Xamla/xamla_egomo/egomo_3d_printed_parts/egomo-1/xamla_mount_rpi_middle.stl

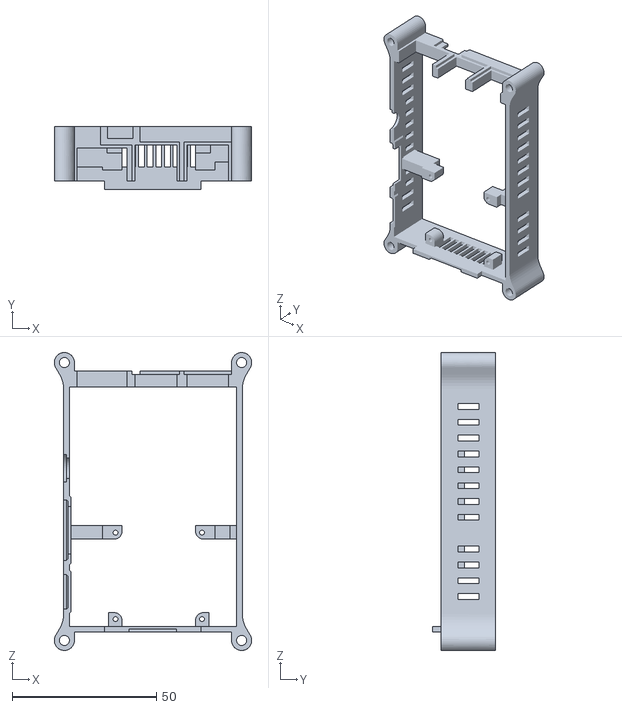
[picture p21: CAD file, 2016-06-17]
egomo_3d_printed_parts/egomo-1/xamla_mount_rpi_middle.stl
68.5 x 21.8 x 103.4
