Xamla/xamla_egomo/egomo_ur5/meshes/robotiq-2-finger-85/collision/gripper_finger_left_1.stl

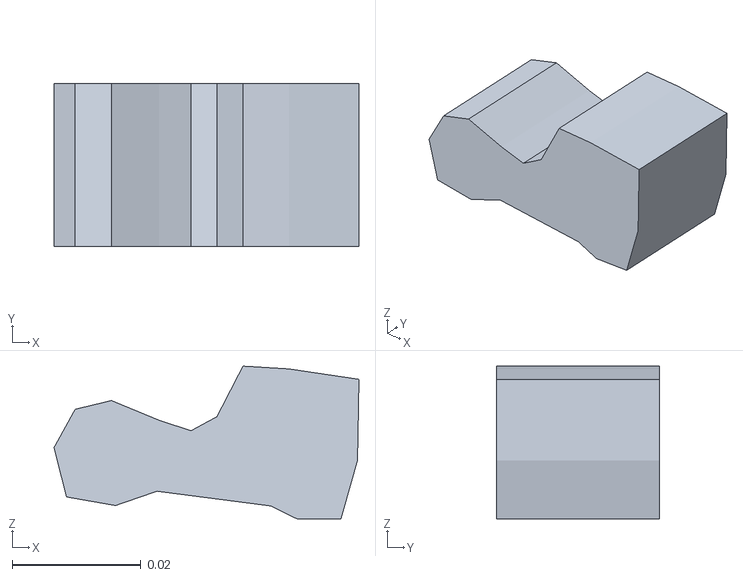
[picture p22: CAD file, 2016-05-12]
egomo_ur5/meshes/robotiq-2-finger-85/collision/gripper_finger_left_1.stl
0.0474 x 0.0254 x 0.0237
