Xamla/xamla_egomo/egomo_ur5/meshes/ur5/collision/wrist_2.stl

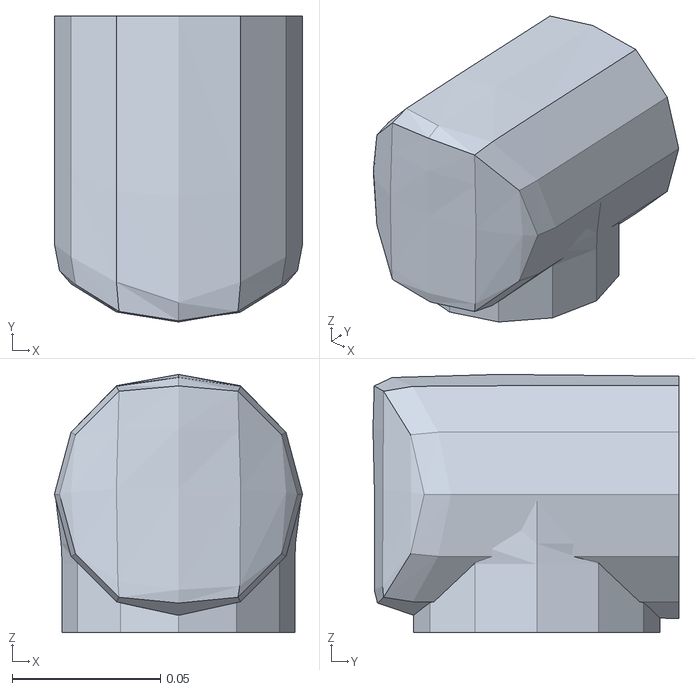
[picture p23: CAD file, 2016-05-12]
egomo_ur5/meshes/ur5/collision/wrist_2.stl
0.0837 x 0.103 x 0.0871
