Xamla/xamla_egomo/egomo_3d_printed_parts/egomo-1/xamla_mount_rpi_bottom.stl

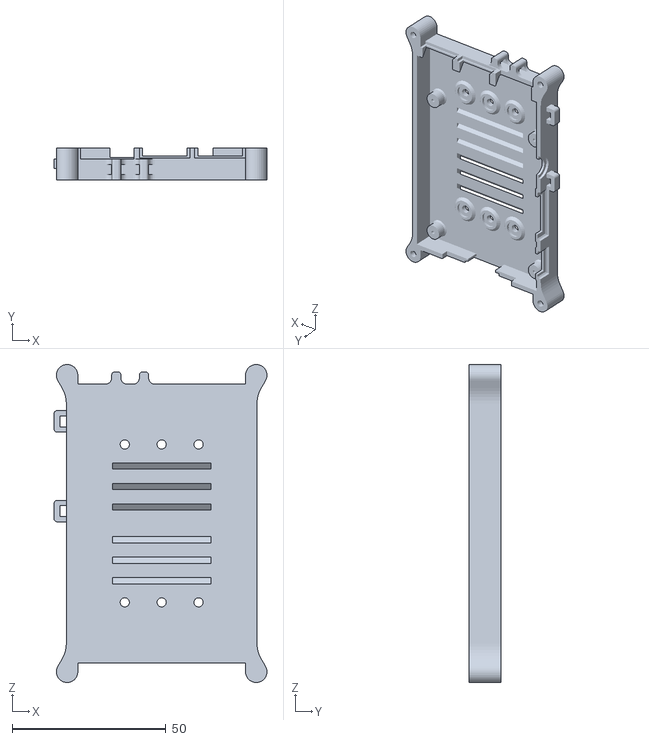
[picture p24: CAD file, 2016-06-17]
egomo_3d_printed_parts/egomo-1/xamla_mount_rpi_bottom.stl
69.2 x 10.3 x 103.4
