Xamla/xamla_egomo/egomo_ur5/meshes/robotiq-2-finger-85/collision/gripper_base.stl

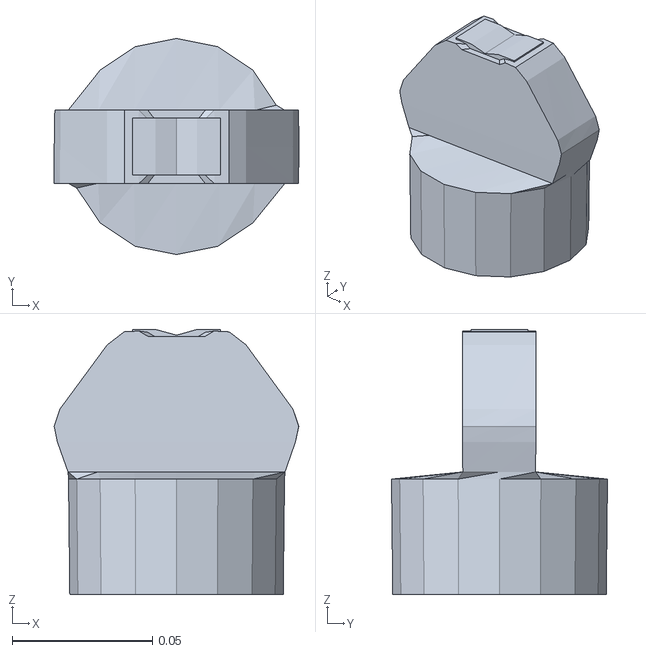
[picture p25: CAD file, 2016-05-12]
egomo_ur5/meshes/robotiq-2-finger-85/collision/gripper_base.stl
0.0874 x 0.0771 x 0.0946
