Xamla/xamla_egomo/egomo_ur5/meshes/ur5/collision/forearm.stl

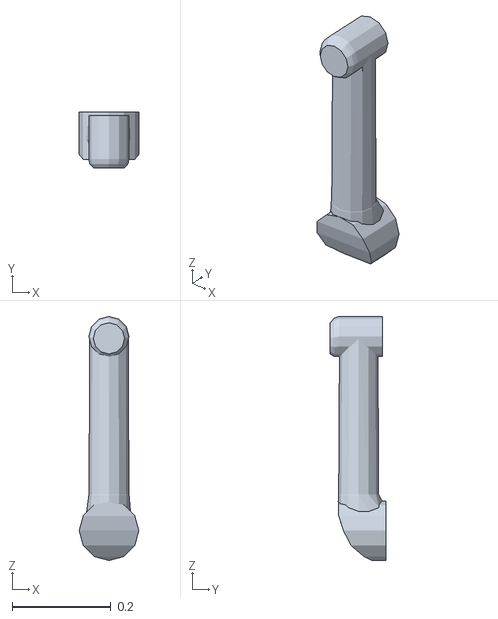
[picture p26: CAD file, 2016-05-12]
egomo_ur5/meshes/ur5/collision/forearm.stl
0.121 x 0.112 x 0.493
