Xamla/xamla_egomo/egomo_3d_printed_parts/egomo-1/xamla_mount_c920_front_0_right.stl

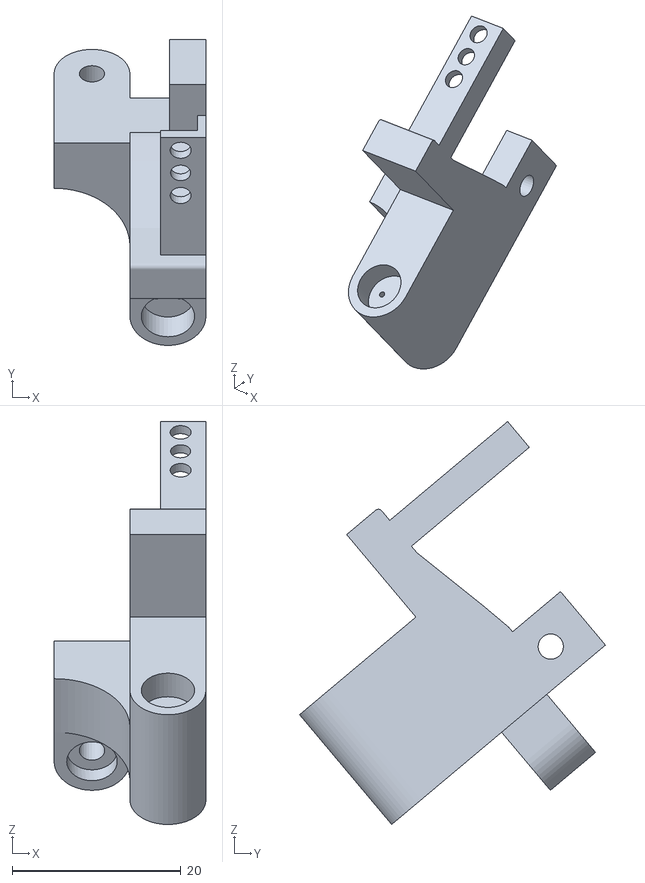
[picture p27: CAD file, 2016-06-17]
egomo_3d_printed_parts/egomo-1/xamla_mount_c920_front_0_right.stl
18.0 x 36.3 x 47.8
