Xamla/xamla_egomo/egomo_ur5/meshes/robotiq-2-finger-85/collision/gripper_finger_left_3.stl

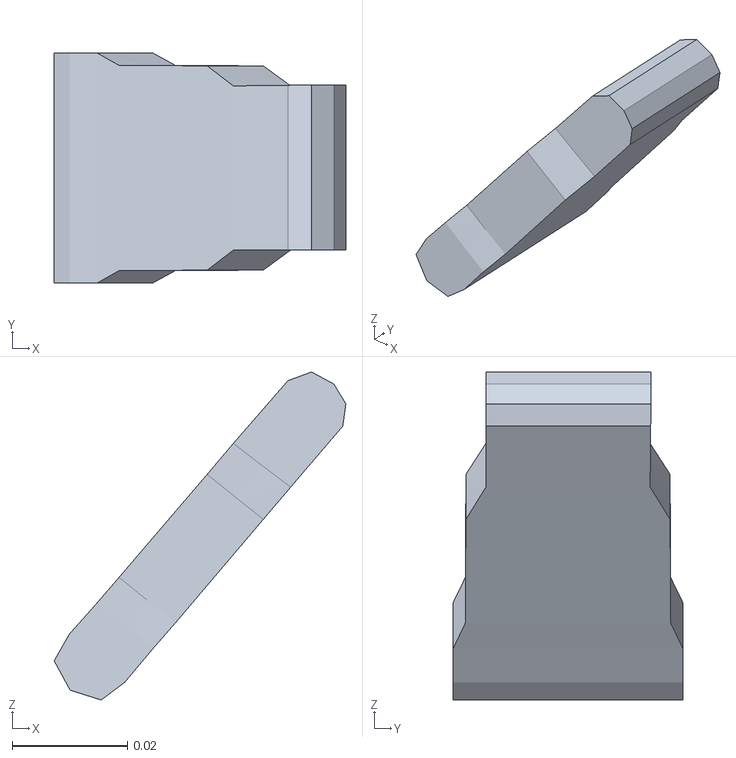
[picture p28: CAD file, 2016-05-12]
egomo_ur5/meshes/robotiq-2-finger-85/collision/gripper_finger_left_3.stl
0.0506 x 0.0398 x 0.0569
