Xamla/xamla_egomo/egomo_ur5/meshes/ur5/collision/wrist_1.stl

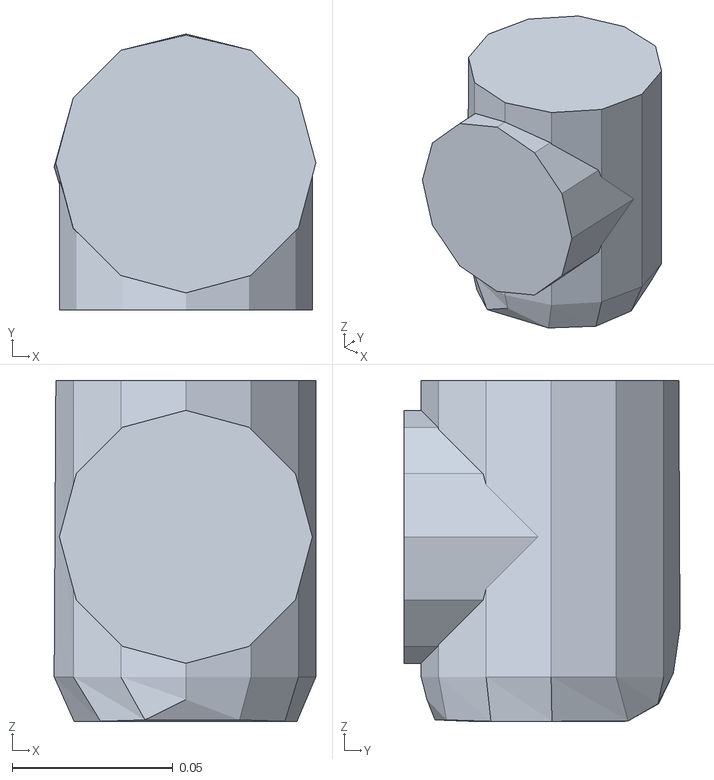
[picture p29: CAD file, 2016-05-12]
egomo_ur5/meshes/ur5/collision/wrist_1.stl
0.0815 x 0.0859 x 0.106
