Xamla/xamla_egomo/egomo_3d_printed_parts/egomo-1/xamla_cap_hole.stl

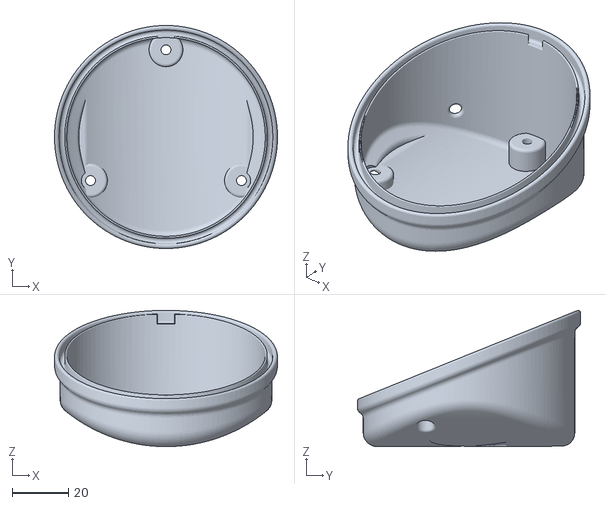
[picture p30: CAD file, 2016-06-17]
egomo_3d_printed_parts/egomo-1/xamla_cap_hole.stl
79.0 x 79.0 x 48.3
