Xamla/xamla_egomo/egomo_ur5/meshes/robotiq-2-finger-85/collision/gripper_finger_left_2.stl

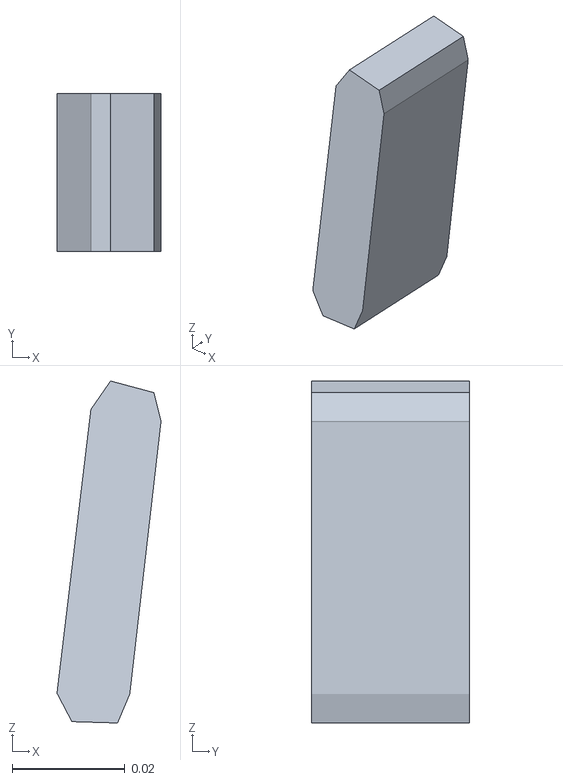
[picture p31: CAD file, 2016-05-12]
egomo_ur5/meshes/robotiq-2-finger-85/collision/gripper_finger_left_2.stl
0.0185 x 0.028 x 0.0607
