Xamla/xamla_egomo/egomo_3d_printed_parts/egomo-1/xamla_mount_c920_right.stl

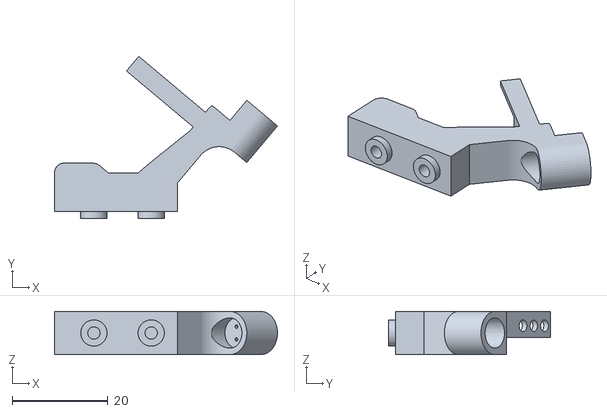
[picture p32: CAD file, 2016-06-17]
egomo_3d_printed_parts/egomo-1/xamla_mount_c920_right.stl
46.7 x 34.0 x 9.02
