Xamla/xamla_egomo/egomo_3d_printed_parts/egomo-1/xamla_mount_flange.stl

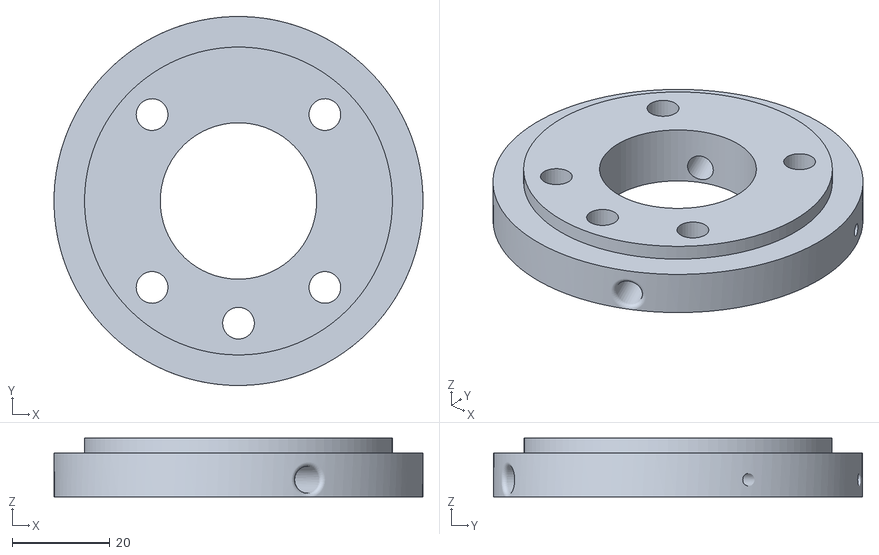
[picture p34: CAD file, 2016-06-17]
egomo_3d_printed_parts/egomo-1/xamla_mount_flange.stl
75.5 x 75.5 x 12.0
