Xamla/xamla_egomo/egomo_docs/Egomo_Installation/small-DSC03187.JPG

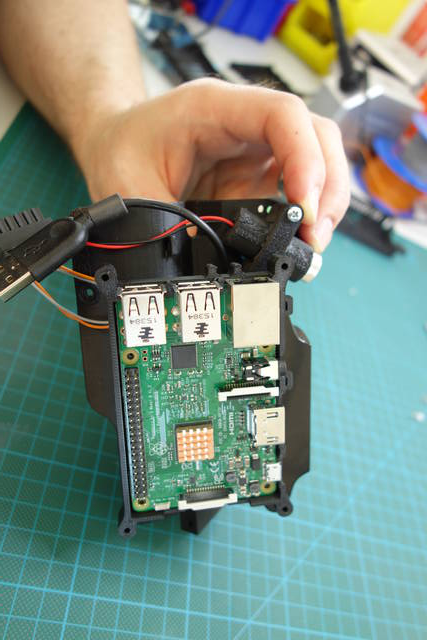
egomo_docs/Egomo_Installation/small-DSC03187.JPG
