Xamla/xamla_egomo/egomo_docs/Egomo_Installation/small-DSC03204.JPG

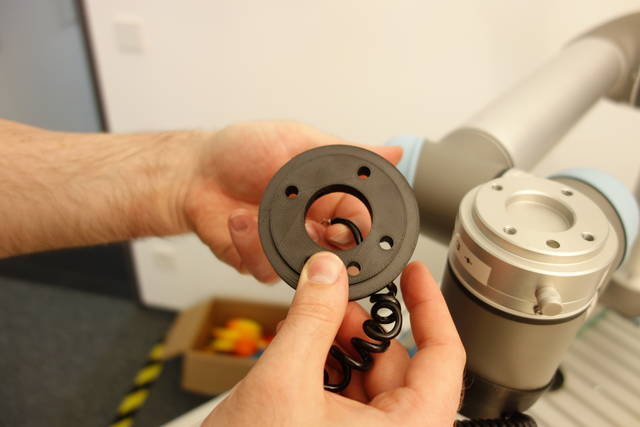
egomo_docs/Egomo_Installation/small-DSC03204.JPG
