Xamla/xamla_egomo/egomo_docs/Egomo_Installation/small-IMG_20160613_182819.jpg

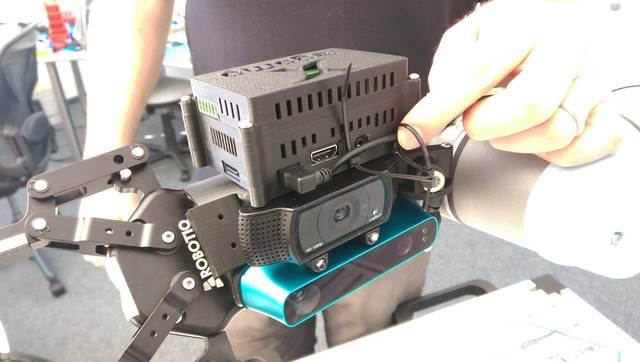
egomo_docs/Egomo_Installation/small-IMG_20160613_182819.jpg
