Xamla/xamla_egomo/egomo_docs/Egomo_Installation/small-IMG_20160613_182855.jpg

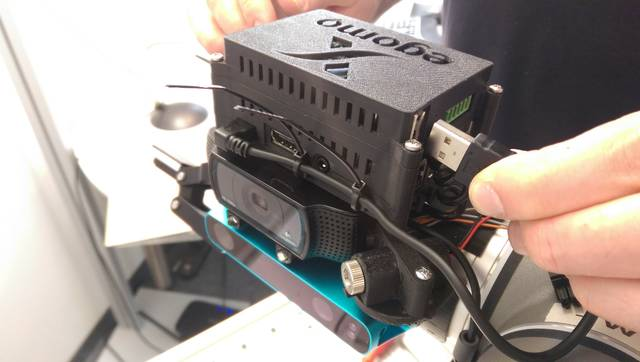
egomo_docs/Egomo_Installation/small-IMG_20160613_182855.jpg
