Xamla/xamla_egomo/egomo_docs/Egomo_Installation/small-IMG_20160613_183529.jpg

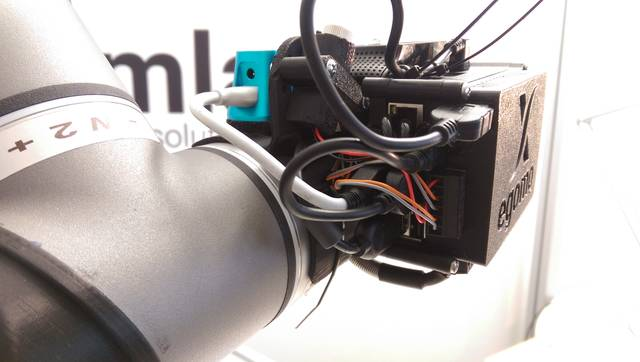
egomo_docs/Egomo_Installation/small-IMG_20160613_183529.jpg
