Xamla/xamla_egomo/egomo_docs/Egomo_Installation/small-IMG_20160613_183718.jpg

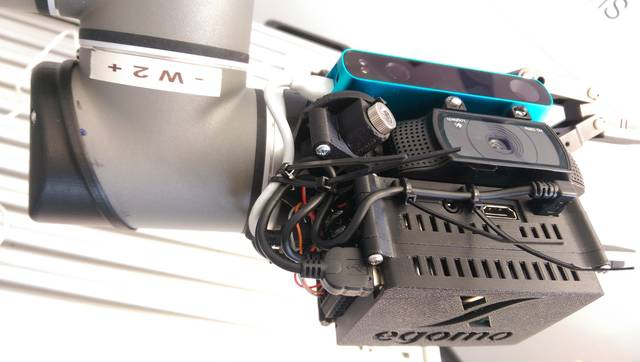
egomo_docs/Egomo_Installation/small-IMG_20160613_183718.jpg
