Xamla/xamla_egomo/egomo_docs/Egomo_Installation/small-rotated-DSC03077.JPG

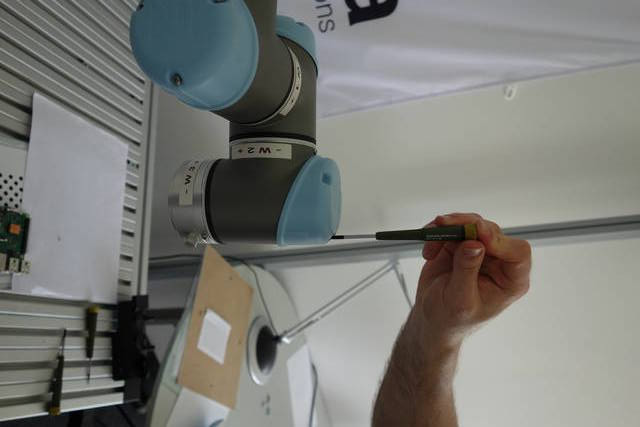
egomo_docs/Egomo_Installation/small-rotated-DSC03077.JPG
