Xamla/xamla_egomo/egomo_docs/Egomo_Installation/small-rotated-DSC03078.JPG

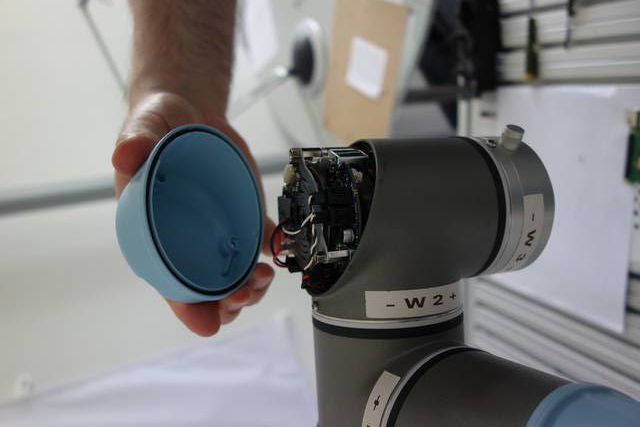
egomo_docs/Egomo_Installation/small-rotated-DSC03078.JPG
