Xamla/xamla_egomo/egomo_docs/Egomo_Installation/small-rotated-DSC03082.JPG

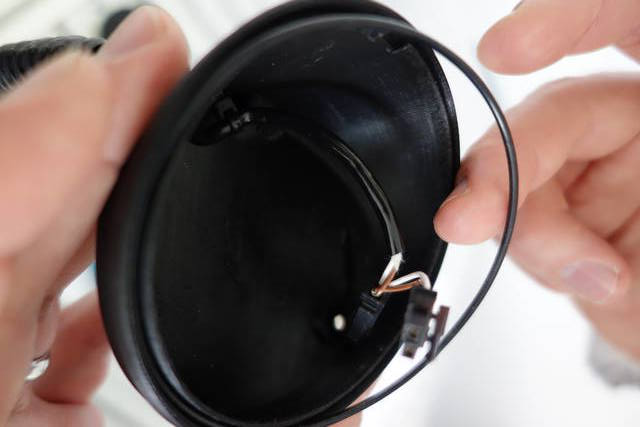
egomo_docs/Egomo_Installation/small-rotated-DSC03082.JPG
