Xamla/xamla_egomo/egomo_docs/Egomo_Installation/small-rotated-IMG_20160613_183912.jpg

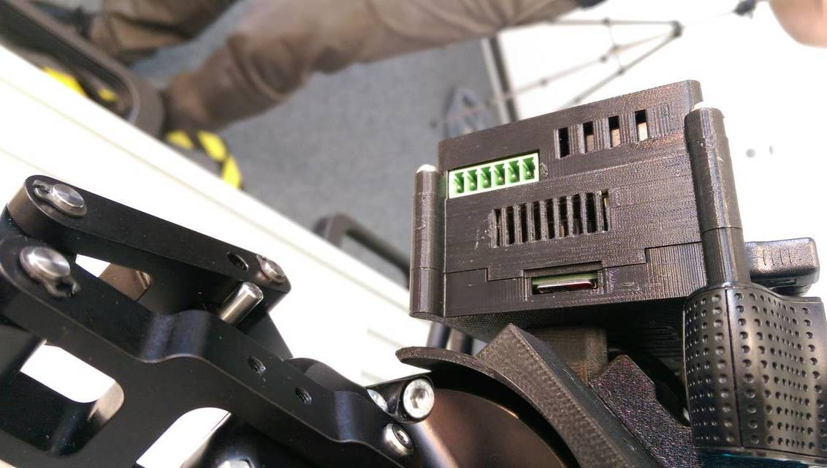
egomo_docs/Egomo_Installation/small-rotated-IMG_20160613_183912.jpg
